alvaroalea/QL_QsoundQprint_clone/INFO/DSCN8382.JPG

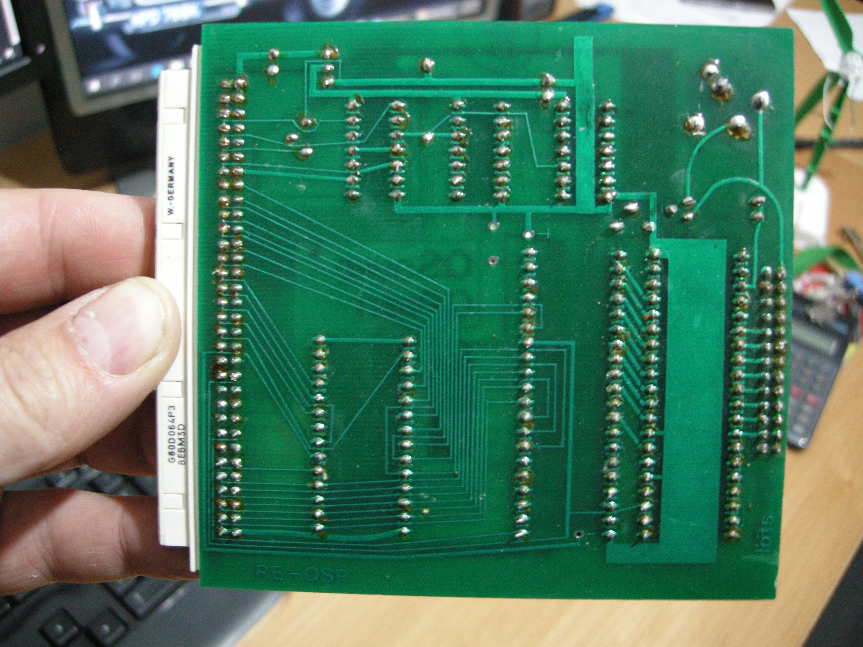
INFO/DSCN8382.JPG
