alvaroalea/QL_QsoundQprint_clone/INFO/DSCN8383.JPG

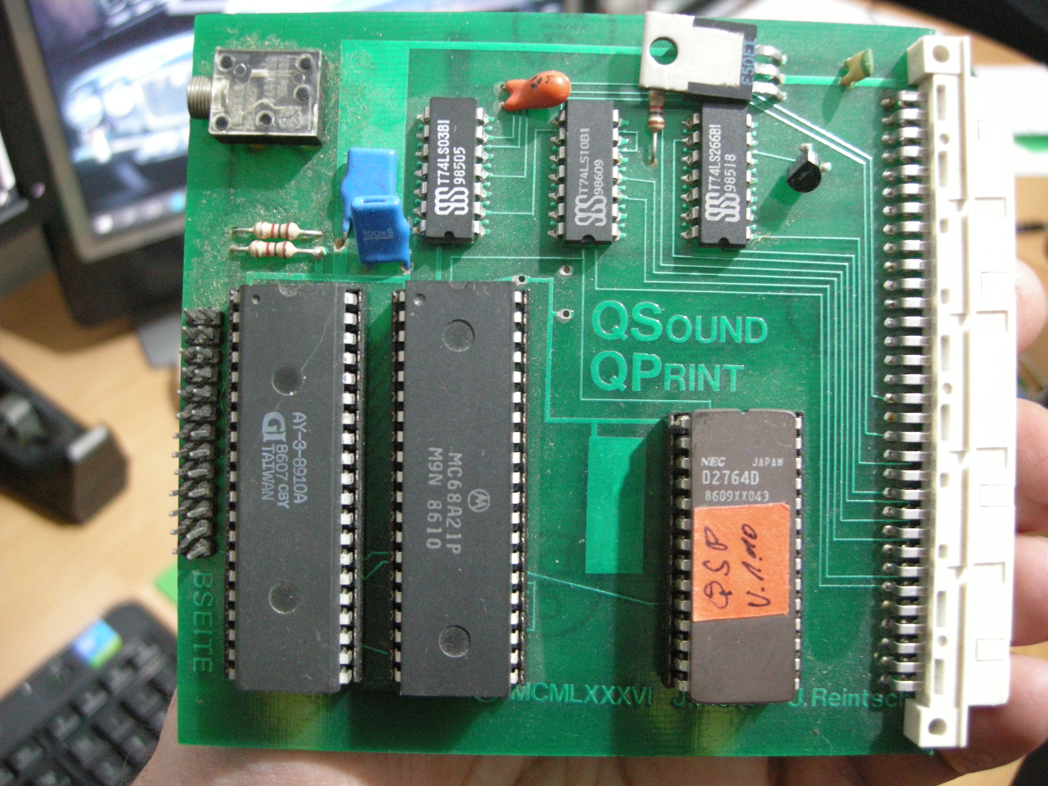
INFO/DSCN8383.JPG
